MGX3D/pegstr/images/_MG_1889.jpg

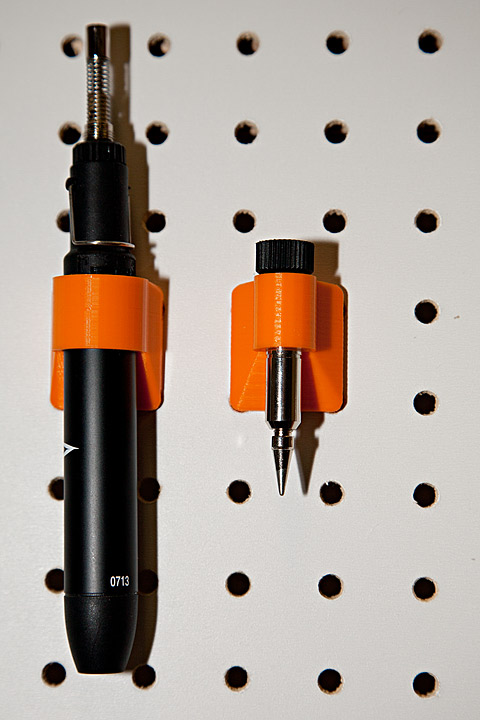
images/_MG_1889.jpg
