MGX3D/pegstr/images/_MG_1918.jpg

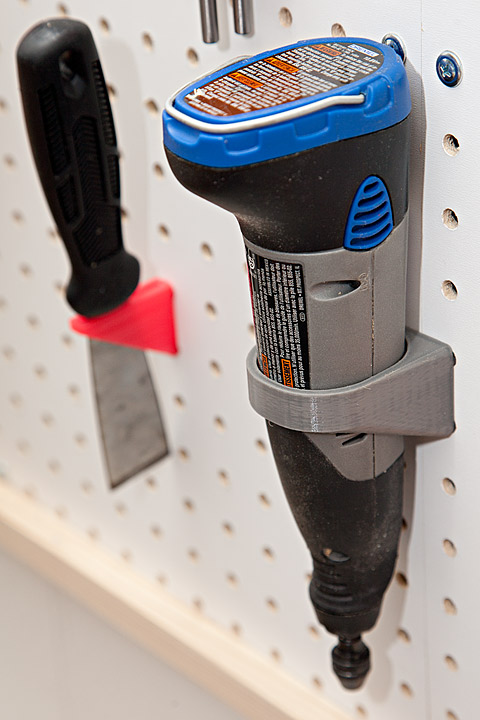
images/_MG_1918.jpg
