MGX3D/pegstr/images/_MG_1920.jpg

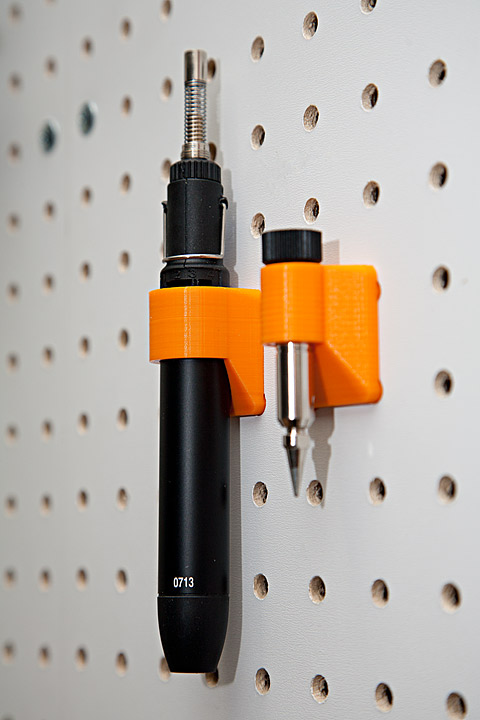
images/_MG_1920.jpg
