MGX3D/pegstr/images/_MG_1949.jpg

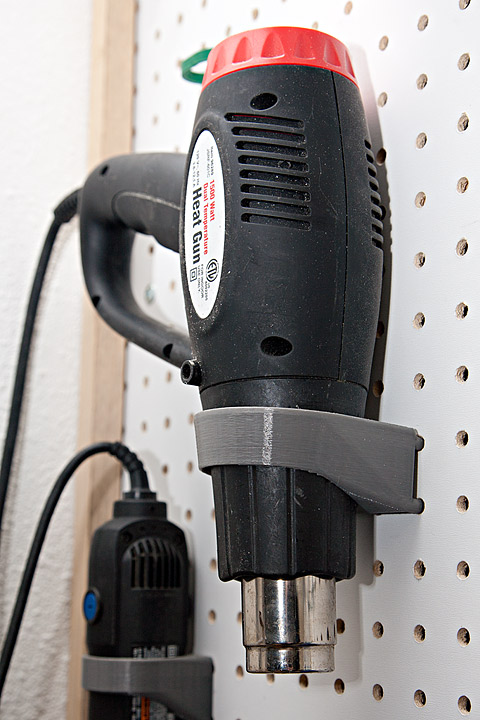
images/_MG_1949.jpg
