MGX3D/pegstr/images/_MG_1950.jpg

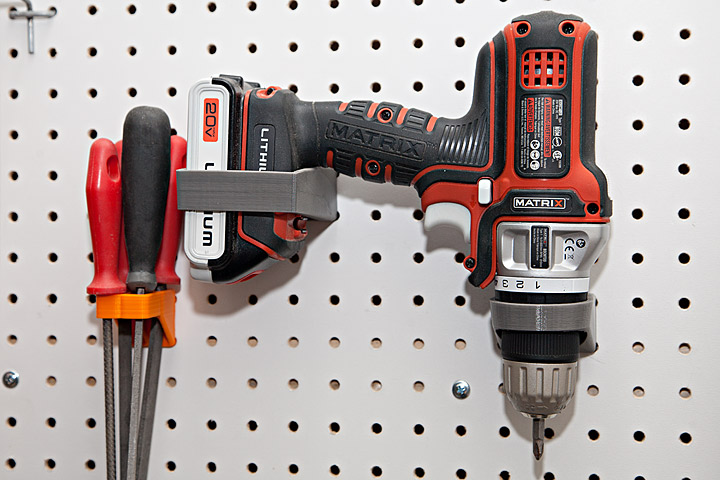
images/_MG_1950.jpg
