MGX3D/pegstr/images/_MG_1968.jpg

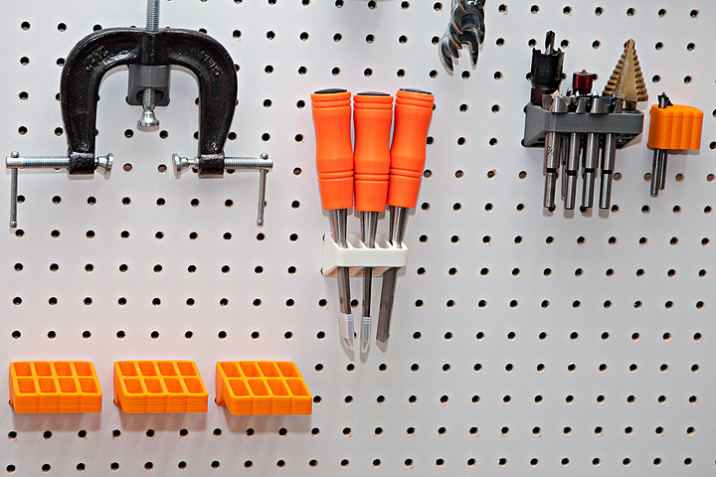
images/_MG_1968.jpg
