MGX3D/pegstr/images/_MG_1970.jpg

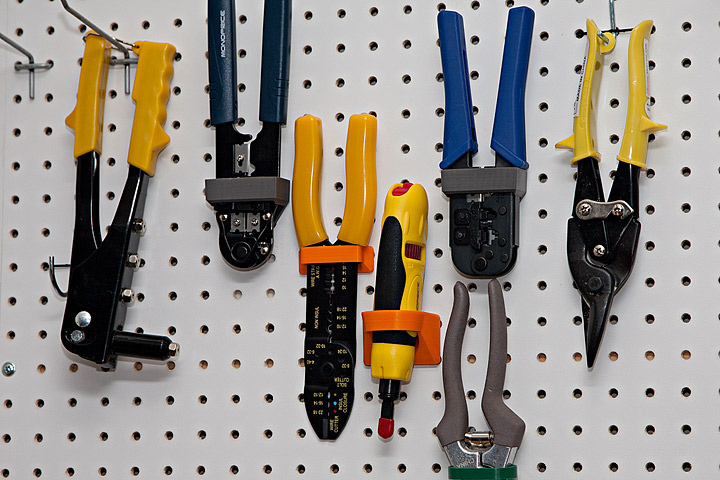
images/_MG_1970.jpg
