MGX3D/pegstr/images/_MG_1983.jpg

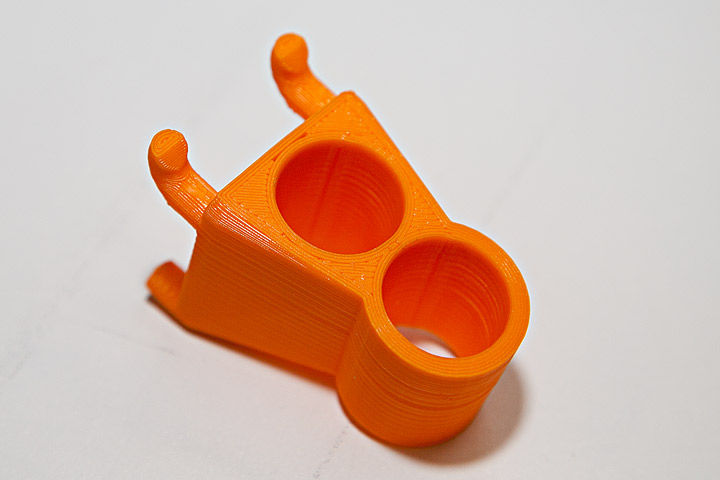
images/_MG_1983.jpg
