MGX3D/pegstr/images/_MG_1986.jpg

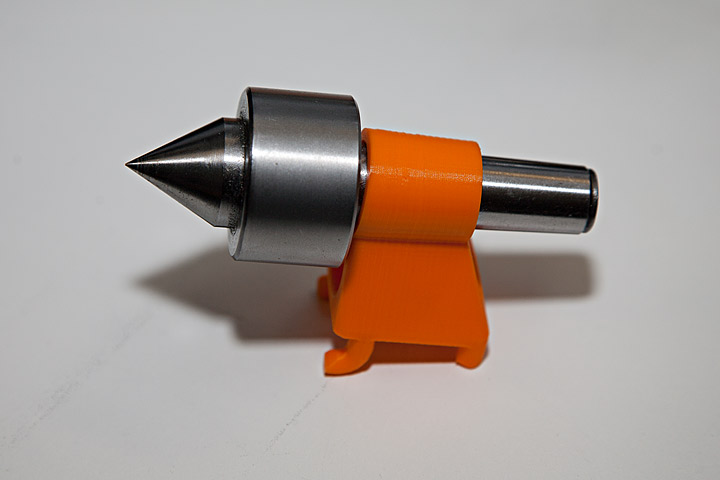
images/_MG_1986.jpg
