MGX3D/pegstr/images/_MG_2008.jpg

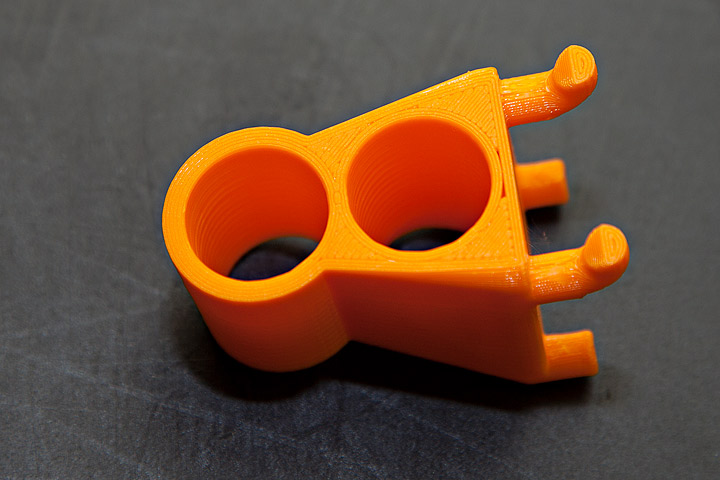
images/_MG_2008.jpg
