MGX3D/pegstr/Samples/PegBoard_box_100x60.stl

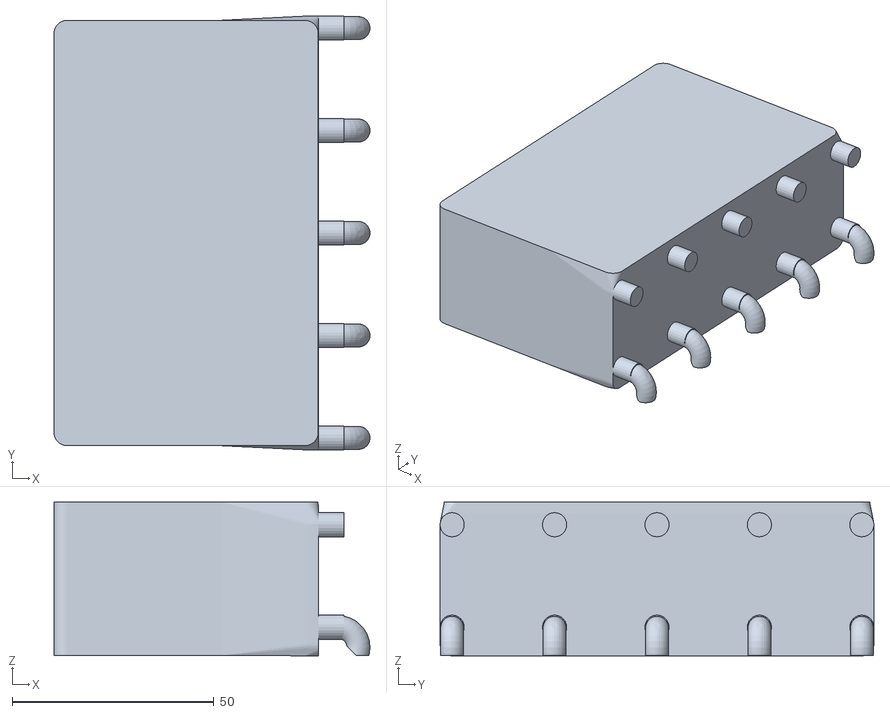
[picture p34: CAD file, 2015-03-20]
Samples/PegBoard_box_100x60.stl
78.4 x 107.6 x 38.1
