MGX3D/pegstr/Samples/PegBoard_2by2_10x10.stl

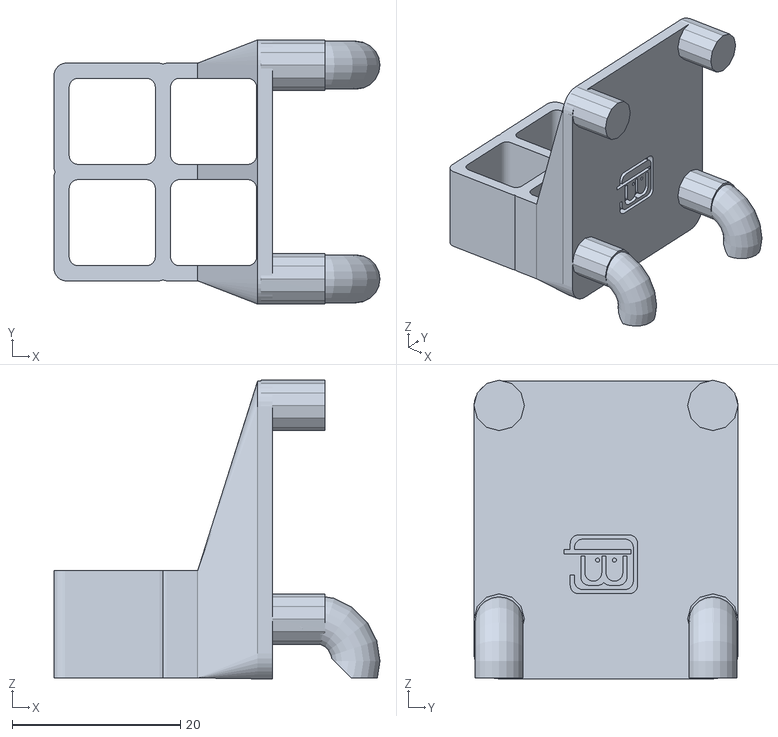
[picture p35: CAD file, 2015-03-20]
Samples/PegBoard_2by2_10x10.stl
38.8 x 31.4 x 35.5
