MGX3D/pegstr/Samples/PegBoard_6by4_10mm.stl

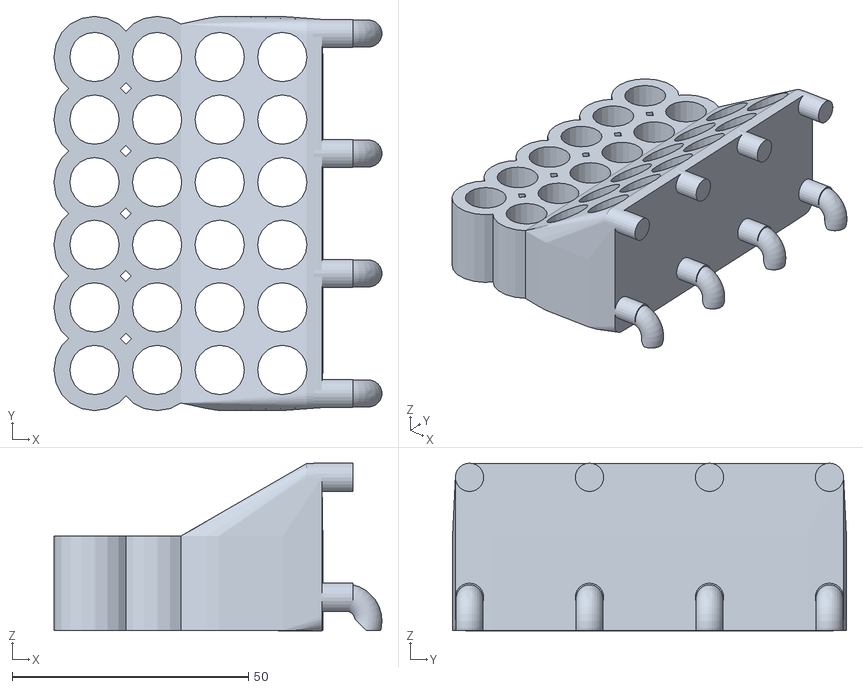
[picture p36: CAD file, 2015-03-20]
Samples/PegBoard_6by4_10mm.stl
69.4 x 83.4 x 35.5
